nigeljohnson73/WRFCOM/data/log_start.png

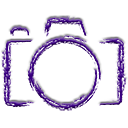
data/log_start.png
