nigeljohnson73/WRFCOM/data/log_stop.png

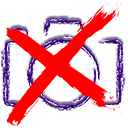
data/log_stop.png
