nigeljohnson73/WRFCOM/data/QR.png

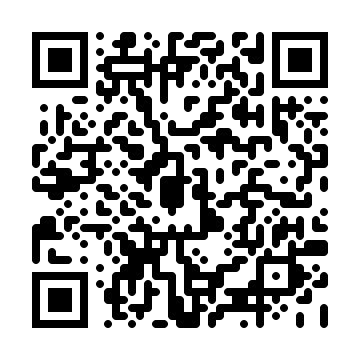
data/QR.png
