nigeljohnson73/WRFCOM/data/srv_arm.png

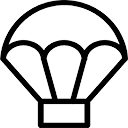
data/srv_arm.png
