nigeljohnson73/WRFCOM/data/srv_disarm.png

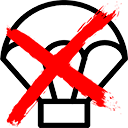
data/srv_disarm.png
