nigeljohnson73/WRFCOM/STL/plates sensors/plate 03 feather.stl

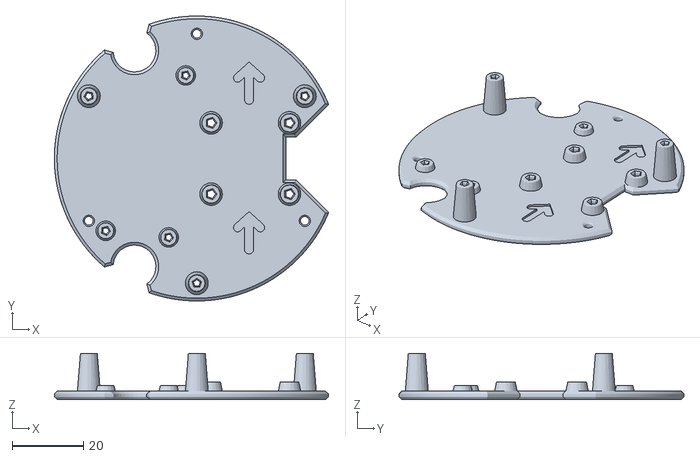
[picture p20: CAD file, 2022-09-07]
STL/plates sensors/plate 03 feather.stl
77.0 x 80.0 x 13.0
