nigeljohnson73/WRFCOM/STL/servo all/servo power box.stl

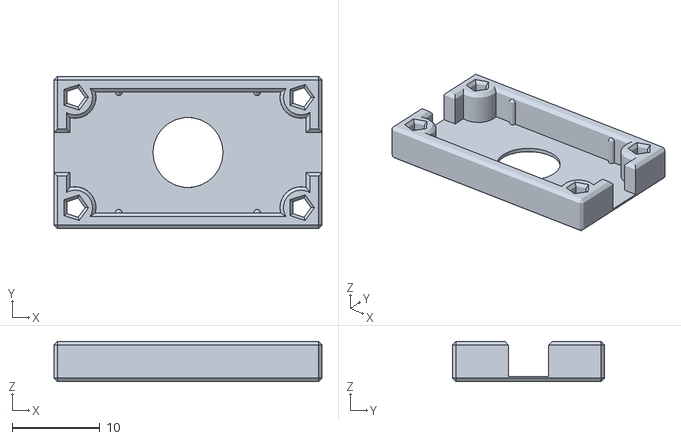
[picture p21: CAD file, 2022-09-07]
STL/servo all/servo power box.stl
30.6 x 17.4 x 4.60
