nigeljohnson73/WRFCOM/STL/plates sensors/plate 02 sensors x4 RTC.stl

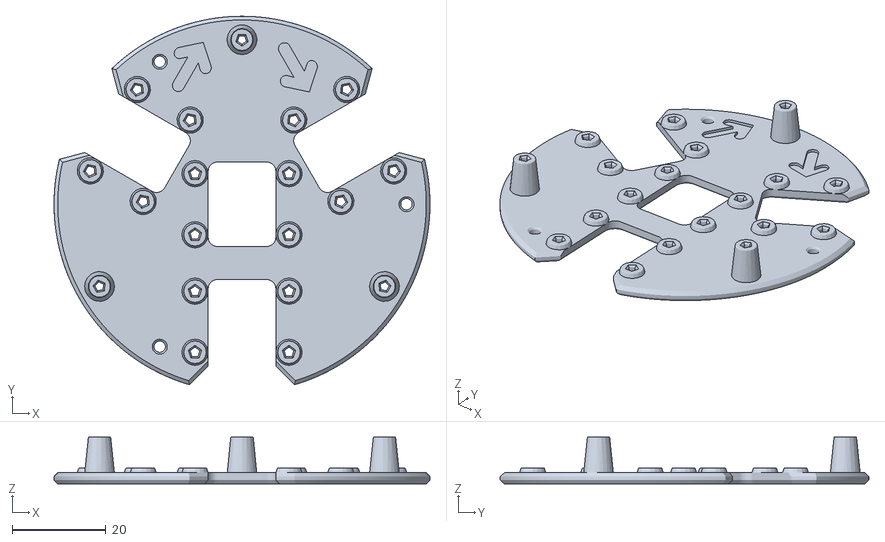
[picture p22: CAD file, 2022-09-07]
STL/plates sensors/plate 02 sensors x4 RTC.stl
80.0 x 78.4 x 9.99
