nigeljohnson73/WRFCOM/STL/servo all/servo pin.stl

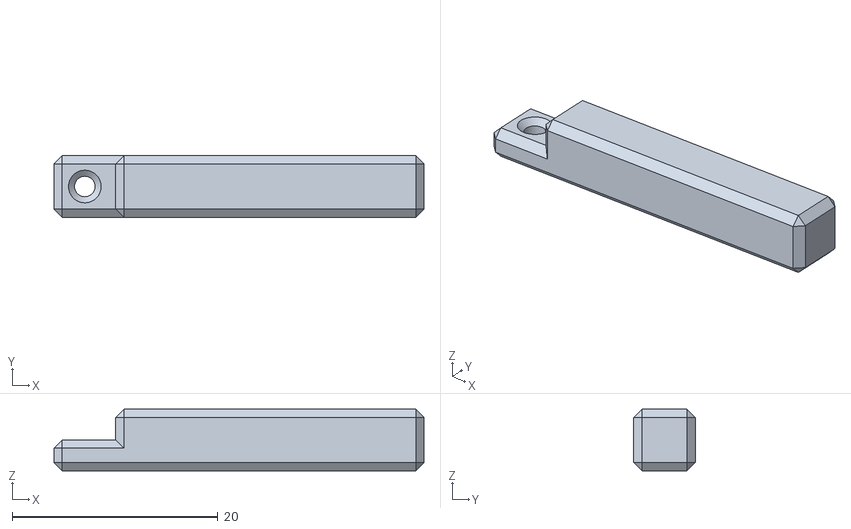
[picture p23: CAD file, 2022-09-07]
STL/servo all/servo pin.stl
36.0 x 6.00 x 6.00
