nigeljohnson73/WRFCOM/STL/servo all/servo cover.stl

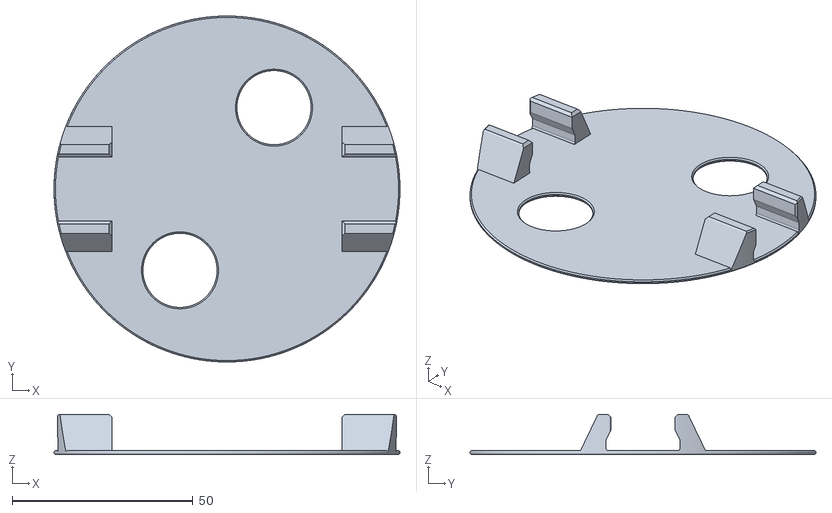
[picture p24: CAD file, 2022-09-07]
STL/servo all/servo cover.stl
95.7 x 95.7 x 11.2
