nigeljohnson73/WRFCOM/WEB.cpp

/***************
   TODO:
   Add handler to set the following parameters
       LOG.setParachuteDeployApogeeOffset(double m);
       LOG.setParachuteDeployDistanceOffset(double m);
       LOG.setLaunchDetectSpeed(double mps);

       EMU.setLocalSeaLevelPressure(double hpa);
       EMU.setLocalTemperature(double c);
*/

#include "WEB.h"
TrWEB WEB;
TrWEB::TrWEB() {};

#if !_USE_WIFI_

void TrWEB::begin() {
#if _DEBUG_ && _DISABLED_DEBUG_
  Serial.println(String("WEB init: disabled");
#endif // _DEBUG_
}

void TrWEB::loop() {}

#else // !_USE_WIFI_

#include "lib/XBase64.h"
#include "lib/XBase64.cpp"

#ifdef ESP32
#include <WiFi.h>
#include <ESPAsyncWebServer.h>
AsyncWebServer WebServer(80);
#else // ESP32
#include <ESP8266WebServer.h>
ESP8266WebServer WebServer(80);
#endif // ESP32



// Adding and manging local URLs for the about page mostly
static const unsigned int pmax = 20;
static unsigned int pcount = 0;
static String urls[pmax];
static String titles[pmax];
static bool _config_updated = false;

AsyncWebServerRequest * __request;

/*******************************************************************************************************************************************
                      dP       .d88888b
                      88       88.    "'
  dP  dP  dP .d8888b. 88d888b. `Y88888b. .d8888b. 88d888b. dP   .dP .d8888b. 88d888b.
  88  88  88 88ooood8 88'  `88       `8b 88ooood8 88'  `88 88   d8' 88ooood8 88'  `88
  88.88b.88' 88.  ... 88.  .88 d8'   .8P 88.  ... 88       88 .88'  88.  ... 88
  8888P Y8P  `88888P' 88Y8888'  Y88888P  `88888P' dP       8888P'   `88888P' dP
*/
void serverBegin() {
  WebServer.begin();
}

#ifdef ESP32
void registerUri(String uri, ArRequestHandlerFunction func) {
  WebServer.on(uri.c_str(), HTTP_GET, func);
}
#else // ESP32
void registerUri(String uri, void (*func)(void)) {
  WebServer.on(uri, func);
}
#endif // ESP32

#ifdef ESP32
void registerNotFound(ArRequestHandlerFunction func) {
#else // ESP32
void registerNotFound(void (*func)(void)) {
#endif // ESP32
  WebServer.onNotFound(func);
}

String getUri() {
#ifdef ESP32
  if (__request) {
    return __request->url();
  } else {
    return "/unknown";
  }
#else // ESP32
  return WebServer.uri();
#endif // ESP32
}

void serverResponse(int code, String type, const char * content, size_t len) {
#ifdef ESP32
  if (__request) {

#if _DEBUG_ && _XDEBUG_
    Serial.print("serverResponse(<binary data>): ");
    Serial.print(len);
    Serial.print(" bytes being sent");
    Serial.println();
#endif // _DEBUG_ && _XDEBUG_

    // This only sends a code 200. The input code is redundant
    AsyncResponseStream *response = __request->beginResponseStream(type, len);
    for (size_t i = 0; i < len; i++) {
      response->write(pgm_read_byte(content + i));
    }
    __request->send(response);
  }
#else // ESP32
  // TBD
#endif // ESP32
}

void serverResponse(int code, String type, String content) {
#ifdef ESP32
  if (__request) {
    __request->send(code, type, content);
    //serverResponse(code, type, (uint8_t *)content.c_str(), content.length());
  }
#else // ESP32
  WebServer.send(code, type, content);
#endif // ESP32
}

void serverLoop() {
#ifdef ESP32
  // It's all handled in the background
#else // ESP32
  WebServer.handleClient();
#endif // ESP32
}

/*******************************************************************************************************************************************
  dP     dP          oo  888888ba                    oo            dP                       dP   oo
  88     88              88    `8b                                 88                       88
  88     88 88d888b. dP a88aaaa8P' .d8888b. .d8888b. dP .d8888b. d8888P 88d888b. .d8888b. d8888P dP .d8888b. 88d888b.
  88     88 88'  `88 88  88   `8b. 88ooood8 88'  `88 88 Y8ooooo.   88   88'  `88 88'  `88   88   88 88'  `88 88'  `88
  Y8.   .8P 88       88  88     88 88.  ... 88.  .88 88       88   88   88       88.  .88   88   88 88.  .88 88    88
  `Y88888P' dP       dP  dP     dP `88888P' `8888P88 dP `88888P'   dP   dP       `88888P8   dP   dP `88888P' dP    dP
                                                 .88
                                             d8888P
*/

#ifdef ESP32
void addPage(String uri, ArRequestHandlerFunction func, String title, bool hidden) {
#else // ESP32
void addPage(String uri, void (*func)(void), String title, bool hidden) {
#endif // ESP32

#if _DEBUG && _XDEBUG_
  Serial.print("WebServer::addPage(");
  Serial.print(uri);
  if (hidden) Serial.print(", hidden");
  else Serial.print(String(", '") + title + "'");
  Serial.print("): called");
  Serial.println();
#endif // _DEBUG_ && _XDEBUG_

  if (!hidden) {
    titles[pcount] = title;
    urls[pcount++] = uri;
  }

  registerUri(uri, func);
}

#ifdef ESP32
void addPage(String uri, ArRequestHandlerFunction func, String title) {
#else // ESP32
void addPage(String uri, void (*func)(void), String title) {
#endif // ESP32
  addPage(uri, func, title, false);
}

#ifdef ESP32
void addPage(String uri, ArRequestHandlerFunction func) {
#else // ESP32
void addPage(String uri, void (*func)(void)) {
#endif // ESP32
  addPage(uri, func, "", true);
}

/*******************************************************************************************************************************************
  dP     dP    dP              dP  888888ba
  88     88    88              88  88    `8b
  88aaaaa88a d8888P 88d8b.d8b. 88 a88aaaa8P' .d8888b. .d8888b. .d8888b.
  88     88    88   88'`88'`88 88  88        88'  `88 88'  `88 88ooood8
  88     88    88   88  88  88 88  88        88.  .88 88.  .88 88.  ...
  dP     dP    dP   dP  dP  dP dP  dP        `88888P8 `8888P88 `88888P'
                                                           .88
                                                       d8888P
*/
void goToUrl(String url) {
  String ret = "";

  ret += "<!DOCTYPE html><html>";
  ret += "<head>";
  ret += "<title>redirection</title>";
  ret += "</head> ";
  ret += "<body>";
  ret += "<script>";
  ret += "window.location.href='";
  ret += url;
  ret += "';";
  ret += "</script>";
  ret += "</body></html>";

  serverResponse(200, "text/html", ret.c_str());
}

String htmlHeader(String title) {
  String ret = "";

  ret += "<!DOCTYPE html><html>";
  ret += "<head>";
  ret += "<meta name='viewport' content='width=device-width, initial-scale=1'>";
  ret += "<title>";
  ret += title;
  ret += "</title>";

  ret += "<link rel='shortcut icon' href='/favicon.png' type='image/png' />";
  ret += "<link rel='apple-touch-icon' href='/favicon.png' />";
  ret += "<style>";

  ret += "html, body {height: 100%;}";
  ret += "body {display:flex; flex-direction: column; background-color: #eee; font-family: Arial, Helvetica, Sans-Serif; color: #090; text-align: center;}";
  ret += "#main {flex: 1 0 auto; padding-bottom: 10px; padding-left: 30px;padding-right: 30px; }";
  ret += "img.responsive {max-width: 100%; height: auto; }";
  ret += "footer {flex-shrink: 0;padding-bottom: 20px;}";
  ret += ".status-wrapper {clear: both;}";
  ret += ".status-wrapper .label, .status-wrapper .value {padding-top: 10px; padding-bottom: 10px; width: 49.5%; float: left; margin-bottom: 10px;}";
  ret += ".status {width: 99%; margin-bottom: 10px; padding-top: 10px; padding-bottom: 10px; border-radius: 5px; border: solid 1px #000; background-color: #ddd; color: #000;}";
  ret += "button{all:unset; width: 99%; margin-bottom: 10px; padding-top: 10px; padding-bottom: 10px; border-radius: 5px; border: solid 1px #060; background-color: #090; color: #fff;}";
  ret += "footer button {float: left; width: ";
  ret += floor(98 / pcount) - 2;
  ret += "%; margin-left:1%; margin-right:1%;}";
  ret += "footer button.selected {background-color:#ccc; border-color: #aaa;}";
  ret += ".status-red {border-color: #a00; background-color: #faa; color: #a00;}";
  ret += ".status-amber {border-color: #a70; background-color: #fca; color: #a70;}";
  ret += ".status-green {border-color: #0a0; background-color: #afa; color: #0a0;}";
  ret += ".status-disabled {border-color: #aaa; background-color: #ddd; color: #fff;}";
  ret += "footer .action {display:none;}";
  ret += "pre#log-summary {margin-top:2px; padding-top: 10px; padding-bottom: 10px; padding-left: 10px;padding-right: 10px; border:solid #666 1px; border-radius:5px; background-color:#e3e3e3; color:#666;}";
  ret += "a#logstat {margin-top:7px;}";
  ret += ".label_wrapper {margin-bottom:10px;}";
  ret += ".message {width: 99%; margin-bottom: 10px; padding-top: 10px; padding-bottom: 10px; border-radius: 5px; border: solid 1px #000; background-color: #ddd; color: #000;}";
  ret += ".message-ok {border-color: #0a0; background-color: #afa; color: #0a0;}";

  ret += " </style> ";

  ret += "<script>";
  ret += "function hideActions() { document.getElementById('footer-buttons').style.display = 'none'; document.getElementById('footer-action').style.display = 'inline-block'; document.getElementById('actions').style.display = 'none'; document.getElementById('log-summary').style.display = 'none';};";
  ret += "function submitConfig() {hideActions(); document.getElementById('config_details').submit();};";
  ret += "</script>";

  ret += " </head> ";
  ret += "<body><div id='main'>";

  return ret;
}

String htmlFooter() {
  String content = "";

  content += "</div><footer>";
  content += "<div id='footer-buttons'>";
  String this_uri = getUri();
  for (int i = 0; i < pcount; i++) {
    content += "<button";
    if (urls[i] == this_uri) {
      content += " class='selected'";
    }
    content += " onclick='window.location.href=\"";
    content += urls[i];
    content += "\"; hideActions();'>";
    content += titles[i];
    content += "</button>";
  }
  content += "</div>";
  content += "<p id='footer-action' class='action'>Please wait...</p>";
  content += "</footer></body></html> ";

  return content;
}

String htmlPage(String title, String content) {
  return htmlHeader(title) + content + htmlFooter();
}

/*******************************************************************************************************************************************
           dP                           888888ba             dP    88888888b                                  dP
           88                           88    `8b            88    88                                         88
  .d8888b. 88d888b. .d8888b. dP  dP  dP 88     88 .d8888b. d8888P a88aaaa    .d8888b. dP    dP 88d888b. .d888b88
  Y8ooooo. 88'  `88 88'  `88 88  88  88 88     88 88'  `88   88    88        88'  `88 88    88 88'  `88 88'  `88
        88 88    88 88.  .88 88.88b.88' 88     88 88.  .88   88    88        88.  .88 88.  .88 88    88 88.  .88
  `88888P' dP    dP `88888P' 8888P Y8P  dP     dP `88888P'   dP    dP        `88888P' `88888P' dP    dP `88888P8

*/

#ifdef ESP32
void showNotFound(AsyncWebServerRequest * request) {
  __request = request;
#else // ESP32
void showNotFound() {
#endif // ESP32

#if _DEBUG_
  String uri = getUri();
  Serial.print("WebServer::showNotFound(");
  Serial.print(uri);
  Serial.print("): called");
  Serial.println();
#endif
  String content = "<h1>Ooopsie... </h1> <p>Well, we looked everywhere, but we don't seem to have found that. Sorry.</p>";
#if _DEBUG_ && _XDEBUG_
  Serial.println("WebServer::showNotFound(): responding");
#endif // _DEBUG_ && _XDEBUG_

  serverResponse(404, "text/html", htmlPage("Ooops", content));
#if _DEBUG && _XDEBUG_
  Serial.println("WebServer::showNotFound(): complete");
#endif // _DEBUG_ && _XDEBUG_
}

/*******************************************************************************************************************************************
           dP                           .d88888b    dP              dP
           88                           88.    "'   88              88
  .d8888b. 88d888b. .d8888b. dP  dP  dP `Y88888b. d8888P .d8888b. d8888P .d8888b.
  Y8ooooo. 88'  `88 88'  `88 88  88  88       `8b   88   88'  `88   88   Y8ooooo.
        88 88    88 88.  .88 88.88b.88' d8'   .8P   88   88.  .88   88         88
  `88888P' dP    dP `88888P' 8888P Y8P   Y88888P    dP   `88888P8   dP   `88888P'
*/

#ifdef ESP32
void showStats(AsyncWebServerRequest * request) {
  __request = request;
#else // EPS32
void showStats() {
#endif // ESP32

#if _DEBUG_
  Serial.println("WebServer::showStats(): called");
#endif // _DEBUG_
  String title;
  String status;
  String text;
  String content = "<h1>Data Snapshot</h1>";

#if _USE_NTP_
  title = "NET Timestamp";
  status = "green";
  text = NET.getTimestamp();
  if (text.length() == 0) {
    status = "disabled";
    text = "[not configured]";
  }
  content += "<div class='status-wrapper'><div class='label'>" + title + "</div><div class='status value status-" + status + "'>" + text + "</div></div>";
#endif

#if _USE_RTC_
  title = "RTC Timestamp";
  status = "green";
  text = RTC.getTimestamp();
  if (!RTC.isEnabled()) {
    status = "disabled";
    text = "[disconnected]";
  } else if (text.length() == 0) {
    status = "red";
    text = "[not configured]";
  }
  content += "<div class='status-wrapper'><div class='label'>" + title + "</div><div class='status value status-" + status + "'>" + text + "</div></div>";
#endif

  title = "GPS Timestamp";
  status = "green";
  text = GPS.getTimestamp();
  if (!GPS.isEnabled()) {
    status = "disabled";
    text = "[disconnected]";
  } else if (text.length() == 0) {
    status = "amber";
    text = "[not locked]";
  }
  content += "<div class='status-wrapper'><div class='label'>" + title + "</div><div class='status value status-" + status + "'>" + text + "</div></div>";

#if IMU_TYPE != IMU_NONE
  title = "IMU Temperature";
  status = "green";
  text = String(IMU.getTemperature());
  if (!IMU.isEnabled()) {
    status = "disabled";
    text = "[disconnected]";
  } else if (text.length() == 0) {
    status = "red";
    text = "[not configured]";
  } else {
    text += " C";
  }
  content += "<div class='status-wrapper'><div class='label'>" + title + "</div><div class='status value status-" + status + "'>" + text + "</div></div>";
#endif

#if EMU_TYPE != EMU_NONE
  title = "EMU Temperature";
  status = "green";
  text = String(EMU.getTemperature());
  if (!EMU.isEnabled()) {
    status = "disabled";
    text = "[disconnected]";
  } else if (text.length() == 0) {
    status = "red";
    text = "[not configured]";
  } else {
    text += " C";
  }
  content += "<div class='status-wrapper'><div class='label'>" + title + "</div><div class='status value status-" + status + "'>" + text + "</div></div>";

  title = "EMU Pressure";
  status = "green";
  text = String(EMU.getPressure());
  if (!EMU.isEnabled()) {
    status = "disabled";
    text = "[disconnected]";
  } else if (text.length() == 0) {
    status = "red";
    text = "[not configured]";
  } else {
    text += " hPa";
    //    text += " (";
    //    text += EMU.getSeaLevelPressure();
    //    text += " MSL)";
  }
  content += "<div class='status-wrapper'><div class='label'>" + title + "</div><div class='status value status-" + status + "'>" + text + "</div></div>";

  title = "EMU Altitude";
  status = "green";
  text = String(EMU.getAltitude());
  if (!EMU.isEnabled()) {
    status = "disabled";
    text = "[disconnected]";
  } else if (text.length() == 0) {
    status = "red";
    text = "[not configured]";
  } else {
    text += " m";
  }
  content += "<div class='status-wrapper'><div class='label'>" + title + "</div><div class='status value status-" + status + "'>" + text + "</div></div>";
#endif

  title = "GPS Altitude";
  status = "green";
  text = "";
  if (!GPS.isEnabled()) {
    status = "disabled";
    text = "[disconnected]";
  } else if (!GPS.isConnected()) {
    status = "amber";
    text = "[not locked]";
  } else {
    text = String(GPS.getAltitude());
    text += " m";
  }
  content += "<div class='status-wrapper'><div class='label'>" + title + "</div><div class='status value status-" + status + "'>" + text + "</div></div>";

  title = "GPS Location";
  status = "green";
  text = "";
  if (!GPS.isEnabled()) {
    status = "disabled";
    text = "[disconnected]";
  } else if (!GPS.isConnected()) {
    status = "amber";
    text = "[not locked]";
  } else {
    text += GPS.getLatitude();
    text += " N, ";
    text += GPS.getLongitude();
    text += " E";
  }
  content += "<div class='status-wrapper'><div class='label'>" + title + "</div><div class='status value status-" + status + "'>" + text + "</div></div>";

  title = "GPS State";
  status = "green";
  int siv = GPS.getSatsInView();
  text = String(GPS.getRefreshRate()) + " Hz, " + String(siv) + " lock" + ((siv == 1) ? "" : "s");
  if (!GPS.isEnabled()) {
    status = "disabled";
    text = "[disconnected]";
  } else if (!GPS.isConnected()) {
    status = "amber";
  }
  content += "<div class='status-wrapper'><div class='label'>" + title + "</div><div class='status value status-" + status + "'>" + text + "</div></div>";



#if _DEBUG_ &&  _XDEBUG_
  Serial.println("WebServer::showStats(): responding");
#endif // _DEBUG_ && _XDEBUG_

  serverResponse(200, "text/html", htmlPage(String(DEVICE_NAME) + " - Stats", content));

#if _DEBUG_ &&  _XDEBUG_
  Serial.println("WebServer::showStats(): complete");
#endif // _DEBUG_ && _XDEBUG_
}

/*******************************************************************************************************************************************

           dP                            .d888888  dP                           dP
           88                           d8'    88  88                           88
  .d8888b. 88d888b. .d8888b. dP  dP  dP 88aaaaa88a 88d888b. .d8888b. dP    dP d8888P
  Y8ooooo. 88'  `88 88'  `88 88  88  88 88     88  88'  `88 88'  `88 88    88   88
        88 88    88 88.  .88 88.88b.88' 88     88  88.  .88 88.  .88 88.  .88   88
  `88888P' dP    dP `88888P' 8888P Y8P  88     88  88Y8888' `88888P' `88888P'   dP
*/
#ifdef ESP32
void showAbout(AsyncWebServerRequest * request) {
  __request = request;
#else // ESP32
void showAbout() {
#endif // ESP32

#if _DEBUG_
  Serial.println("WebServer::showAbout(): called");
#endif // _DEBUG_

  String content = "<h1>About ";
  content += DEVICE_NAME;
  content += "</h1>";
  content += "<div>";
  content += String("<p>Application Version: ") + VERSION + "</p>";
  content += String("<p>Application Build: ") + __DATE__ + " @ " + __TIME__ + "</p>";
  content += "<p>A Nigel Johnson <a href='https://github.com/nigeljohnson73/WRFCOM'>Github project</a>.</p>";
  content += "</div>";
  content += "<div>";
  content += "<img src='aboutqr.png' alt='QR Code for project' class='responsive'/>";
  content += "</div>";

#if _DEBUG_ &&  _XDEBUG_
  Serial.println("WebServer::showAbout(): responding");
#endif // _DEBUG_ && _XDEBUG_

  serverResponse(200, "text/html", htmlPage(String(DEVICE_NAME) + " - About", content));

#if _DEBUG_ &&  _XDEBUG_
  Serial.println("WebServer::showAbout(): complete");
#endif // _DEBUG_ && _XDEBUG_
}

/*******************************************************************************************************************************************
           dP                            888888ba                      dP
           88                            88    `8b                     88
  .d8888b. 88d888b. .d8888b. dP  dP  dP a88aaaa8P' .d8888b. .d8888b. d8888P
  Y8ooooo. 88'  `88 88'  `88 88  88  88  88   `8b. 88'  `88 88'  `88   88
        88 88    88 88.  .88 88.88b.88'  88     88 88.  .88 88.  .88   88
  `88888P' dP    dP `88888P' 8888P Y8P   dP     dP `88888P' `88888P'   dP
*/
#ifdef ESP32
void showRoot(AsyncWebServerRequest* request) {
  __request = request;
#else // ESP32
void showRoot() {
#endif // ESP32

#if _DEBUG_
  Serial.println("WebServer::showRoot(): called");
#endif // _DEBUG_
  String content = String("<h2>") + DEVICE_NAME + "</h2>";
  String status = "";
  String text = "";

#if EMU_TYPE != EMU_NONE
  status = "red";
  text = "DISABLED";
  if (EMU.isEnabled()) {
    status = "green";
    text = "OK";
  };
  content += "<div class='status-wrapper'><div class='label'>EMU</div><div class='status value status-" + status + "'>" + text + "</div></div>";
#endif

#if IMU_TYPE != IMU_NONE
  status = "red";
  text = "DISABLED";
  if (IMU.isEnabled()) {
    status = "green";
    text = "OK";
  };
  content += "<div class='status-wrapper'><div class='label'>IMU</div><div class='status value status-" + status + "'>" + text + "</div></div>";
#endif

  //#if _USE_RTC_
  //  status = "red";
  //  text = "DISABLED";
  //  if (RTC.isEnabled()) {
  //    status = "green";
  //    text = "OK";
  //  };
  //  content += "<div class='status-wrapper'><div class='label'>RTC</div><div class='status value status-" + status + "'>" + text + "</div></div>";
  //#endif

#if _USE_BMS_
  status = "disabled";
  text = "DISABLED";
  if (BMS.isEnabled()) {
    double pcnt = BMS.getCapacityPercent();
    double volt = BMS.getCapacityVoltage();
    text = String(volt) + "v, " + String(pcnt) + "%";
    if (pcnt <= 10) {
      status = "red";
    } else if (pcnt <= 30) {
      status = "amber";
    } else {
      status = "green";
    }
  };
  content += "<div class='status-wrapper'><div class='label'>BMS</div><div class='status value status-" + status + "'>" + text + "</div></div>";
#endif // _USE_BMS_

#if _USE_SERVO_
  status = "disabled";
  text = "DISABLED";
  if (SRV.isEnabled()) {
    if (SRV.isArmed()) {
      status = "green";
      text = "ARMED";
    } else {
      status = "amber";
      text = "DISARMED";
    }
  };
  content += "<div class='status-wrapper'><div class='label'>SRV</div><div class='status value status-" + status + "'>" + text + "</div></div>";
#endif // _USE_SERVO_

  status = "red";
  text = "DISABLED";
  if (GPS.isEnabled()) {
    status = "amber";
    text = "NOT LOCKED";
    if (GPS.isConnected()) {
      status = "green";
      text = "LOCKED";
    };
  }
  content += "<div class='status-wrapper'><div class='label'>GPS</div><div class='status value status-" + status + "'>" + text + "</div></div>";

  status = "red";
  text = "DISABLED";
  if (LOG.isEnabled()) {
    if (LOG.isCapturing()) {
      status = "green";
      text = "LOGGING";
    } else {
      status = "amber";
      text = "IDLE";
    }
  };
  content += "<div class='status-wrapper'><div class='label'>LOG</div><div class='status value status-" + status + "'>" + text + "</div></div>";

  content += "<div style='clear:both'></div>";
  content += "<div id='actions'>";
  if (LOG.isCapturing()) {
    content += "<button onclick='window.location.href=\"/api/log/stop\"; hideActions();'>Stop Capture</button>";
  } else {
    if (LOG.isEnabled()) {
      content += "<button onclick='window.location.href=\"/api/log/start\"; hideActions();'>Start Capture</button>";
    }
    if (SRV.isEnabled()) {
      if (SRV.isArmed()) {
        content += "<button onclick='window.location.href=\"/api/srv/disarm\"; hideActions();'>Disarm</button>";
      } else {
        content += "<button onclick='window.location.href=\"/api/srv/arm\"; hideActions();'>Arm</button>";
      }
    }
    //    content += "<button onclick='window.location.href=\"/cfg\"; hideActions();'>Config</button>";
  }

  content += "</div>";

  //  content += "<img alt='logo' src='/favicon.png' />";

  String log_summary = LOG.getLogSummary();
  content += "<div>";
  if (log_summary.length() > 0) {
    content += "<pre id='log-summary'>";
    content += log_summary;
    content += "</pre>";
  }
  content += "</div>";
#if _DEBUG_ &&  _XDEBUG_
  Serial.println("WebServer::showRoot(): responding");
#endif // _DEBUG_ && _XDEBUG_

  serverResponse(200, "text/html", htmlPage(String(DEVICE_NAME) + " - Home", content));

#if _DEBUG_ &&  _XDEBUG_
  Serial.println("WebServer::showRoot(): complete");
#endif // _DEBUG_ && _XDEBUG_
}

/*******************************************************************************************************************************************
           dP                            a88888b.                   .8888b oo
           88                           d8'   `88                   88   "
  .d8888b. 88d888b. .d8888b. dP  dP  dP 88        .d8888b. 88d888b. 88aaa  dP .d8888b.
  Y8ooooo. 88'  `88 88'  `88 88  88  88 88        88'  `88 88'  `88 88     88 88'  `88
        88 88    88 88.  .88 88.88b.88' Y8.   .88 88.  .88 88    88 88     88 88.  .88
  `88888P' dP    dP `88888P' 8888P Y8P   Y88888P' `88888P' dP    dP dP     dP `8888P88
                                                                                   .88
                                                                               d8888P
*/
#ifdef ESP32
void showConfig(AsyncWebServerRequest* request) {
  __request = request;
#else // ESP32
void showConfig() {
#endif // ESP32

#if _DEBUG_
  Serial.println("WebServer::showConfig(): called");
#endif // _DEBUG_
  String content = "<h2>Config - ";
  content += DEVICE_NAME;
  content += "</h2>";

  if (_config_updated) {
    // Show a message
    content += "<div class='message message-ok'>Configuration Updated</div>";
  }
  _config_updated = false;

  content += "<form id='config_details' action='/api/cfg/update'>";

  content += "<div class='label_wrapper'>";
  content += "<label for='apogee_offset'>Deploy Apogee Offset (m):</label>";
  content += "<input  type='number' id='apogee_offset' name='apogee_offset' value='";
  content += LOG.getParachuteDeployApogeeOffset();
  content += "'>";
  content += "</div>";

  content += "<div class='label_wrapper'>";
  content += "<label for='distance_offset'>Deploy Distance Offset (m):</label>";
  content += "<input  type='number' id='distance_offset' name='distance_offset' value='";
  content += LOG.getParachuteDeployDistanceOffset();
  content += "'>";
  content += "</div>";

  content += "<div class='label_wrapper'>";
  content += "<label for='launch_detect_speed'>Launch Detect Speed (m/s):</label>";
  content += "<input  type='number' id='launch_detect_speed' name='launch_detect_speed' value='";
  content += LOG.getLaunchDetectSpeed();
  content += "'>";
  content += "</div>";

#if EMU_TYPE != EMU_NONE
  content += "<div class='label_wrapper'>";
  content += "<label for='msl_hpa'>Sea Level Pressure (hPa):</label>";
  content += "<input  type='number' id='msl_hpa' name='msl_hpa' value='";
  content += EMU.getLocalSeaLevelPressure();
  content += "'>";
  content += "</div>";

  content += "<div class='label_wrapper'>";
  content += "<label for='local_temp'>Local Temperature(C):</label>";
  content += "<input  type='number' id='local_temp' name='local_temp' value='";
  content += EMU.getLocalTemperature();
  content += "'>";
  content += "</div>";
#endif

  content += "<div id='actions'>";
  content += "<button onclick='submitConfig();'>Update</button>";
  content += "</div>";

  content += "</form>";
  content += "<div id='log-summary'></div>";

#if _DEBUG_ &&  _XDEBUG_
  Serial.println("WebServer::showConfig(): responding");
#endif // _DEBUG_ && _XDEBUG_

  serverResponse(200, "text/html", htmlPage(String(DEVICE_NAME) + " - Config", content));

#if _DEBUG_ &&  _XDEBUG_
  Serial.println("WebServer::showConfig(): complete");
#endif // _DEBUG_ && _XDEBUG_
}

/*******************************************************************************************************************************************
  dP                               dP dP          dP
  88                               88 88          88
  88d888b. .d8888b. 88d888b. .d888b88 88 .d8888b. 88        .d8888b. .d8888b.
  88'  `88 88'  `88 88'  `88 88'  `88 88 88ooood8 88        88'  `88 88'  `88
  88    88 88.  .88 88    88 88.  .88 88 88.  ... 88        88.  .88 88.  .88
  dP    dP `88888P8 dP    dP `88888P8 dP `88888P' 88888888P `88888P' `8888P88
                                                                          .88
                                                                      d8888P
*/
#ifdef ESP32
void handle_logStart(AsyncWebServerRequest * request) {
  __request = request;
#else // ESP32
void handle_logStart() {
#endif // ESP32

#if _DEBUG_
  Serial.println("WebServer::handle_logStart(): called");
#endif // _DEBUG_
  LOG.capture(true);
  goToUrl("/");
}

#ifdef ESP32
void handle_logStop(AsyncWebServerRequest * request) {
  __request = request;
#else // ESP32
void handle_logStop() {
#endif // ESP32

#if _DEBUG_
  Serial.println("WebServer::handle_logStop(): called");
#endif // _DEBUG_
  LOG.capture(false);
  goToUrl("/");
}

/*******************************************************************************************************************************************
  dP                               dP dP           .d888888
  88                               88 88          d8'    88
  88d888b. .d8888b. 88d888b. .d888b88 88 .d8888b. 88aaaaa88a 88d888b. 88d8b.d8b.
  88'  `88 88'  `88 88'  `88 88'  `88 88 88ooood8 88     88  88'  `88 88'`88'`88
  88    88 88.  .88 88    88 88.  .88 88 88.  ... 88     88  88       88  88  88
  dP    dP `88888P8 dP    dP `88888P8 dP `88888P' 88     88  dP       dP  dP  dP
*/
#ifdef ESP32
void handle_srvArm(AsyncWebServerRequest * request) {
  __request = request;
#else
void handle_srvArm() {
#endif
#if _DEBUG_
  Serial.println("WebServer::handle_srvArm(): called");
#endif // _DEBUG_
  SRV.arm(true);
  goToUrl("/");
}

#ifdef ESP32
void handle_srvDisarm(AsyncWebServerRequest * request) {
  __request = request;
#else // ESP32
void handle_srvDisarm() {
#endif // ESP32

#if _DEBUG_
  Serial.println("WebServer::handle_srvDisarm(): called");
#endif // _DEBUG_
  SRV.arm(false);
  goToUrl("/");
}

/*******************************************************************************************************************************************
  dP                               dP dP           a88888b.                   .8888b oo
  88                               88 88          d8'   `88                   88   "
  88d888b. .d8888b. 88d888b. .d888b88 88 .d8888b. 88        .d8888b. 88d888b. 88aaa  dP .d8888b.
  88'  `88 88'  `88 88'  `88 88'  `88 88 88ooood8 88        88'  `88 88'  `88 88     88 88'  `88
  88    88 88.  .88 88    88 88.  .88 88 88.  ... Y8.   .88 88.  .88 88    88 88     88 88.  .88
  dP    dP `88888P8 dP    dP `88888P8 dP `88888P'  Y88888P' `88888P' dP    dP dP     dP `8888P88
                                                                                             .88
                                                                                         d8888P
*/
#ifdef ESP32
void handle_configUpdate(AsyncWebServerRequest * request) {
  __request = request;
#else // ESP32
void handle_configUpdate() {
#endif // ESP32

#if _DEBUG_
  Serial.println("WebServer::handle_configUpdate(): called");
#endif // _DEBUG_

  String value;

  if (request->hasParam("apogee_offset")) {
    value = request->getParam("apogee_offset")->value();
    LOG.setParachuteDeployApogeeOffset(abs(value.toFloat()));
#if _DEBUG_
    Serial.print("apogee_offset: ");
    Serial.print(abs(value.toFloat()));
    Serial.println();
  } else {
    Serial.print("apogee_offset: N/A");
    Serial.println();
#endif
  }

  if (request->hasParam("distance_offset")) {
    value = request->getParam("distance_offset")->value();
    LOG.setParachuteDeployDistanceOffset(abs(value.toFloat()));
#if _DEBUG_
    Serial.print("distance_offset: ");
    Serial.print(abs(value.toFloat()));
    Serial.println();
  } else {
    Serial.print("distance_offset: N/A");
    Serial.println();
#endif
  }

  if (request->hasParam("launch_detect_speed")) {
    value = request->getParam("launch_detect_speed")->value();
    LOG.setLaunchDetectSpeed(abs(value.toFloat()));
#if _DEBUG_
    Serial.print("launch_detect_speed: ");
    Serial.print(abs(value.toFloat()));
    Serial.println();
  } else {
    Serial.print("launch_detect_speed: N/A");
    Serial.println();
#endif
  }

  if (request->hasParam("msl_hpa")) {
    value = request->getParam("msl_hpa")->value();
    EMU.setLocalSeaLevelPressure(abs(value.toFloat()));
#if _DEBUG_
    Serial.print("msl_hpa: ");
    Serial.print(abs(value.toFloat()));
    Serial.println();
  } else {
    Serial.print("msl_hpa: N/A");
    Serial.println();
#endif
  }

  if (request->hasParam("local_temp")) {
    value = request->getParam("local_temp")->value();
    EMU.setLocalTemperature(abs(value.toFloat()));
#if _DEBUG_
    Serial.print("local_temp: ");
    Serial.print(abs(value.toFloat()));
    Serial.println();
  } else {
    Serial.print("local_temp: N/A");
    Serial.println();
#endif
  }

  _config_updated = true;
  goToUrl("/cfg");
}

/*******************************************************************************************************************************************
           dP                            88888888b                   dP
           88                            88                          88
  .d8888b. 88d888b. .d8888b. dP  dP  dP a88aaaa    .d8888b. dP   .dP 88 .d8888b. .d8888b. 88d888b.
  Y8ooooo. 88'  `88 88'  `88 88  88  88  88        88'  `88 88   d8' 88 88'  `"" 88'  `88 88'  `88
        88 88    88 88.  .88 88.88b.88'  88        88.  .88 88 .88'  88 88.  ... 88.  .88 88    88
  `88888P' dP    dP `88888P' 8888P Y8P   dP        `88888P8 8888P'   dP `88888P' `88888P' dP    dP
*/
#ifdef ESP32
void showFavIcon(AsyncWebServerRequest * request) {
  __request = request;
#else // ESP32
void showFavIcon() {
#endif // ESP32

#if _DEBUG_
  Serial.println("WebServer::showFavIcon(): called");
#endif // _DEBUG_
  // 64x64
  static char image[] PROGMEM = "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";

  int base64Len = strlen(image);
  int binaryLen = Base64.decodedLength(image, base64Len);

  char binary[binaryLen];
  Base64.decode(binary, image, base64Len);

#if _DEBUG_ &&  _XDEBUG_
  Serial.println("WebServer::showFavIcon(): responding");
#endif // _DEBUG_ && _XDEBUG_

  serverResponse(200, "image/png", binary, binaryLen);

#if _DEBUG_ &&  _XDEBUG_
  Serial.println("WebServer::showFavIcon(): complete");
#endif // _DEBUG_ && _XDEBUG_
}

/*******************************************************************************************************************************************
           dP                            .d888888  dP                           dP    .88888.
           88                           d8'    88  88                           88   d8'   `8b
  .d8888b. 88d888b. .d8888b. dP  dP  dP 88aaaaa88a 88d888b. .d8888b. dP    dP d8888P 88     88  88d888b.
  Y8ooooo. 88'  `88 88'  `88 88  88  88 88     88  88'  `88 88'  `88 88    88   88   88  db 88  88'  `88
        88 88    88 88.  .88 88.88b.88' 88     88  88.  .88 88.  .88 88.  .88   88   Y8.  Y88P  88
  `88888P' dP    dP `88888P' 8888P Y8P  88     88  88Y8888' `88888P' `88888P'   dP    `8888PY8b dP
*/
#ifdef ESP32
void showAboutQr(AsyncWebServerRequest * request) {
  __request = request;
#else // ESP32
void showAboutQr() {
#endif // ESP32

#if _DEBUG_
  Serial.println("WebServer::showAboutQr(): called");
#endif // _DEBUG_
  static char image[] PROGMEM = "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";

  int base64Len = strlen(image);
  int binaryLen = Base64.decodedLength(image, base64Len);

  char binary[binaryLen];
  Base64.decode(binary, image, base64Len);

#if _DEBUG_ && _XDEBUG_
  Serial.println("WebServer::showAboutQr(): responding");
#endif // _DEBUG_ && _XDEBUG_

  serverResponse(200, "image/png", binary, binaryLen);

#if _DEBUG_ && _XDEBUG_
  Serial.println("WebServer::showAboutQr(): complete");
#endif // _DEBUG_ && _XDEBUG_
}

/************************************************************************************************************************************************************
  dP                         oo
  88
  88d888b. .d8888b. .d8888b. dP 88d888b.
  88'  `88 88ooood8 88'  `88 88 88'  `88
  88.  .88 88.  ... 88.  .88 88 88    88
  88Y8888' `88888P' `8888P88 dP dP    dP
                         .88
                     d8888P
*/
void TrWEB::begin() {

  // Public pages visible by default
  addPage("/", showRoot, "Home");
  addPage("/about", showAbout, "About");
  addPage("/stats", showStats, "Stats");
  addPage("/cfg", showConfig, "Config");

  // these pages should not be publically listed, so no title means hidden
  addPage("/favicon.png", showFavIcon);
  addPage("/aboutqr.png", showAboutQr);
  addPage("/api/log/start", handle_logStart);
  addPage("/api/log/stop", handle_logStop);

#if _USE_SERVO_
  // Allow for dervo hndling if enabled
  addPage("/api/srv/arm", handle_srvArm);
  addPage("/api/srv/disarm", handle_srvDisarm);
  addPage("/api/cfg/update", handle_configUpdate);
#endif

  // Add a 404 handler
  registerNotFound(showNotFound);

  // Start the server
  serverBegin();

#if _DEBUG_
  //  Serial.println(String("     Web server: http://") + NET.getIpAddress() + "/");
  Serial.println(String("WEB init: http://") + NET.getIpAddress() + "/");
  if (!NET.isApMode()) {
    Serial.println(String("                 http://") + NET.getHostname() + ".local/");
    //  Serial.println(String("                 http://") + NET.getHostname() + "/");
  }
#endif // _DEBUG_
}

/************************************************************************************************************************************************************
  dP
  88
  88 .d8888b. .d8888b. 88d888b.
  88 88'  `88 88'  `88 88'  `88
  88 88.  .88 88.  .88 88.  .88
  dP `88888P' `88888P' 88Y888P'
                       88
                       dP
*/
void TrWEB::loop() {
  serverLoop();
}

#endif // !_USE_WIFI
