nigeljohnson73/WRFCOM/SRV.cpp

#include "SRV.h"

TrSRV SRV;
TrSRV::TrSRV() {};

#if !_USE_SERVO_

void TrSRV::begin() {
#if _DEBUG_ && _DISABLED_DEBUG_
  Serial.println("SRV init: disabled");
#endif
}

void TrSRV::loop() {}
void TrSRV::arm(bool tf) {}

#else // Using servo

#if ESP32
#ifndef SERVO_PIN
#define SERVO_PIN 12
#endif
#include <ESP32Servo.h>

#else // Not ESP32

#ifndef SERVO_PIN
#define SERVO_PIN D4
#endif
#include <Servo.h>

#endif // ESP32 or not

#define MIN_VAL 700
#define MAX_VAL 2300
#define STOW_ANGLE 110
#define DEPLOY_ANGLE 175

Servo myservo;

void TrSRV::begin() {

#if ESP32
  // Allow allocation of all timers
  ESP32PWM::allocateTimer(0);
  ESP32PWM::allocateTimer(1);
  ESP32PWM::allocateTimer(2);
  ESP32PWM::allocateTimer(3);
  myservo.setPeriodHertz(50);
#endif

  if (!myservo.attach(SERVO_PIN, MIN_VAL, MAX_VAL)) {
#if _DEBUG_
    Serial.println("SRV init: disconnected");
#endif
  }

  _enabled =  true;
  arm(false); // park it to start with

#if _DEBUG_
  Serial.print("SRV init: Stow/Deploy: ");
  Serial.print(STOW_ANGLE);
  Serial.print("/");
  Serial.print(DEPLOY_ANGLE);
  Serial.print(" degrees");
  Serial.println();
#endif
}

void TrSRV::loop() {
}

void TrSRV::arm(bool tf) {
  if (!isEnabled()) return;

  int ang = STOW_ANGLE + (tf ? (DEPLOY_ANGLE - STOW_ANGLE) : 0);
#if _DEBUG_ && _XDEBUG_
  Serial.print("SRV::arm(");
  Serial.print(tf ? "true" : "false");
  Serial.print("): called - ang: ");
  Serial.print(ang);
  Serial.println();
#endif

  myservo.write(ang);
  _armed = tf;
}

#endif //_USE_SERVO_
