nigeljohnson73/WRFCOM/EMU.h

#ifndef _EMU_h
#define _EMU_h

#include "App.h"

class TrEMU {
  public:
    TrEMU();

    void setAltitude(double m); // will calculate sea level pressure based on this passed value
    void begin();
    void loop();
    double getPressure(); // in hPa
    double getTemperature(); // in C
    double getAltitude(); // in m

    bool isEnabled() {
      return _enabled;
    };

    bool hasPressure() {
      return _has_pressure;
    };

    bool hasTemperature() {
      return _has_temperature;
    };

    double getLocalSeaLevelPressure() {
      return _sea_level_pressure;
    }; // in hPa

    void setLocalSeaLevelPressure(double hpa) {
      _sea_level_pressure = hpa;
    };

    double getLocalTemperature() {
      return _local_temperature;
    };

    void setLocalTemperature(double c) {
      _local_temperature = c;
    };

  private:
    bool _enabled = false;
    bool _has_pressure = false;
    bool _has_temperature = false;
    double _sea_level_pressure = 1013.25;
    double _local_temperature = 19.5;
};

extern TrEMU EMU;

#endif
