nigeljohnson73/WRFCOM/LOG.h

#ifndef _LOG_h
#define _LOG_h

#include "App.h"

class TrLOG {
  public:
    TrLOG();

    void begin();
    void loop();
    String getTimestamp();
    String getLogSummary();

    void capture(bool tf); // start or stop the logging
    bool isCapturing() {
      return _logging;
    };
    bool isEnabled() {
      return _enabled;
    };

    double getParachuteDeployApogeeOffset() {
      return _deploy_apogee_offset;
    };

    void setParachuteDeployApogeeOffset(double m) {
      _deploy_apogee_offset = m;
    };

    double getParachuteDeployDistanceOffset() {
      return _deploy_distance_offset;
    };

    void setParachuteDeployDistanceOffset(double m) {
      _deploy_distance_offset = m;
    };

    double getLaunchDetectSpeed() {
      return _launch_detect_speed;
    };

    void setLaunchDetectSpeed(double mps) {
      _launch_detect_speed = mps;
    };

    double getLandingDetectSpeed() {
      return _landing_detect_speed;
    };

    void setLandingDetectSpeed(double mps) {
      _landing_detect_speed = mps;
    };

  protected:
    void resetData();
    void getData();
    void processData();
    void writeHeader();
    void writeData();

    void startCapture();
    void stopCapture();
    void syncLog();
    //    void tidy();

  private:
    long logging_started = 0;
    bool _enabled = false;
    bool _logging = false;

    //    String _log;
    String _log_fn;
    String _log_dir;
    String _log_ts;
    unsigned long _last_sync;
    const unsigned long _sync_interval = 0;// 5000;

    double _deploy_apogee_offset = 2.0;
    double _deploy_distance_offset = 65.0;
    double _launch_detect_speed = 2.5; // ZOE and SAM are only accurate to 2m... and the drift can be 0.15m between capture frames... 
    double _landing_detect_speed = 0.5; // we really need to make sure we are down
    double _emergency_launch_detect_speed = 5; // Once a lock in in place, drift has never been recorded over 4m so 5m/s is a safe mishandling value

};

extern TrLOG LOG;

#endif
